Jaros262/zaverecny_projekt/code/simple_parts/bluetooth/setup/how_to_configure_and_pair_two_hc-05_bluetooth_modules_as_master_and_slave_at_commands_F2QwFNeicx.png

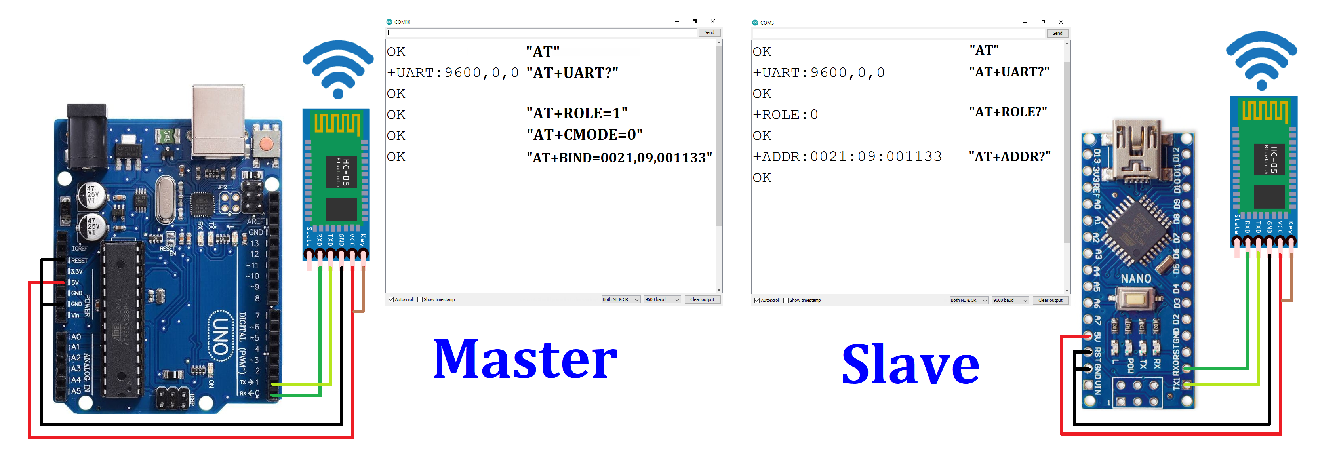
code/simple_parts/bluetooth/setup/how_to_configure_and_pair_two_hc-05_bluetooth_modules_as_master_and_slave_at_commands_F2QwFNeicx.png
