Jaros262/zaverecny_projekt/img_files/v1.1.png

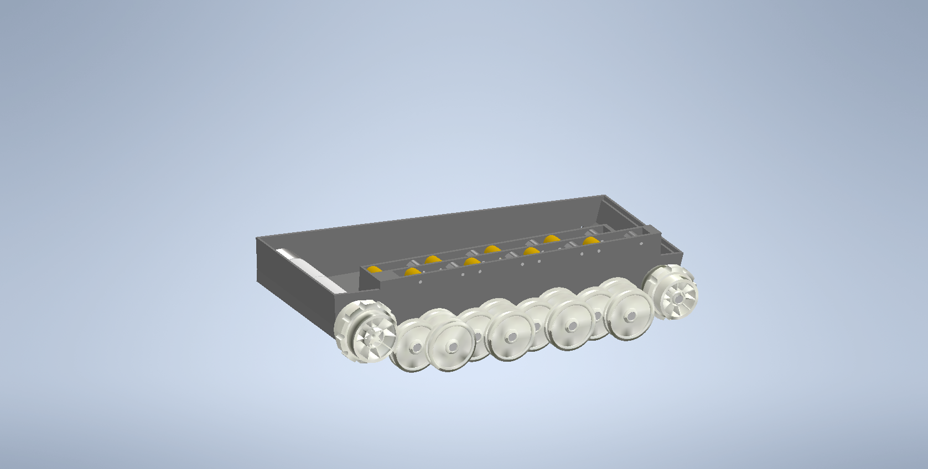
img_files/v1.1.png
