Jaros262/zaverecny_projekt/code/img/principOvladaniMotoru.png

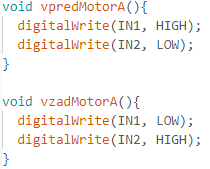
code/img/principOvladaniMotoru.png
