Jaros262/zaverecny_projekt/code/img/principServa.png

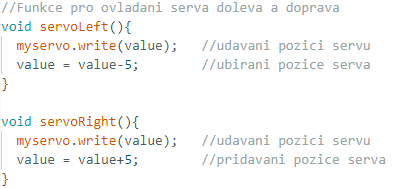
code/img/principServa.png
