Jaros262/zaverecny_projekt/img_files/battery.png

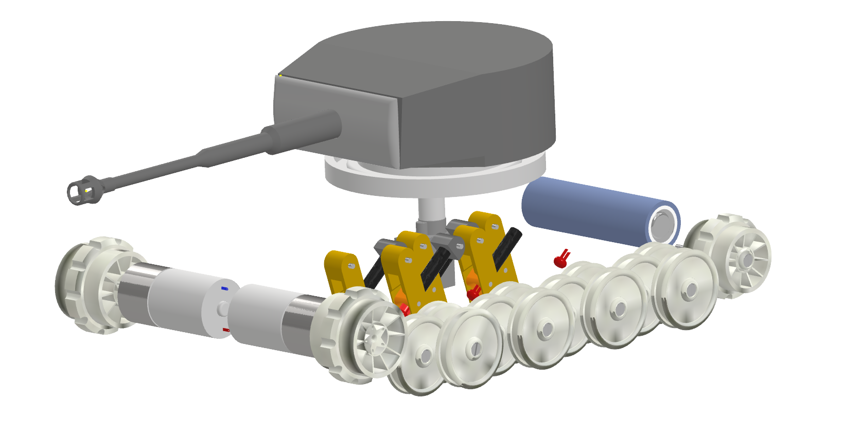
img_files/battery.png
