Jaros262/zaverecny_projekt/img_files/cele-rozdělané.png

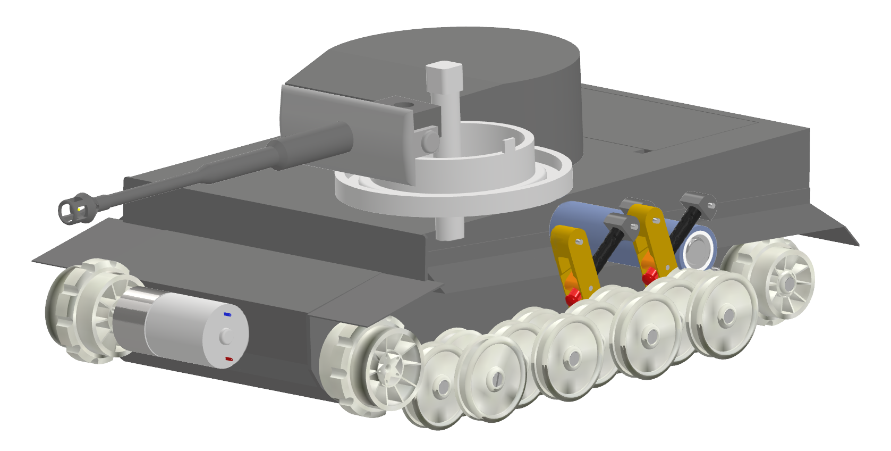
img_files/cele-rozdělané.png
