Jaros262/zaverecny_projekt/img_files/cele-s-popisy.png

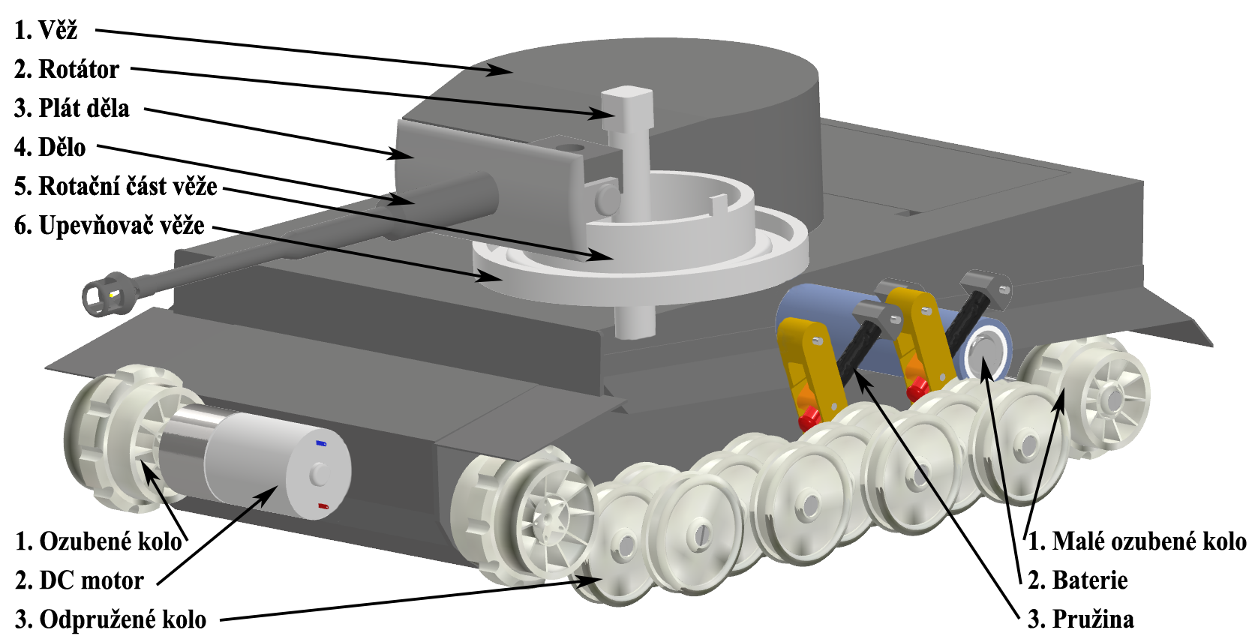
img_files/cele-s-popisy.png
