Jaros262/zaverecny_projekt/img_files/cele.png

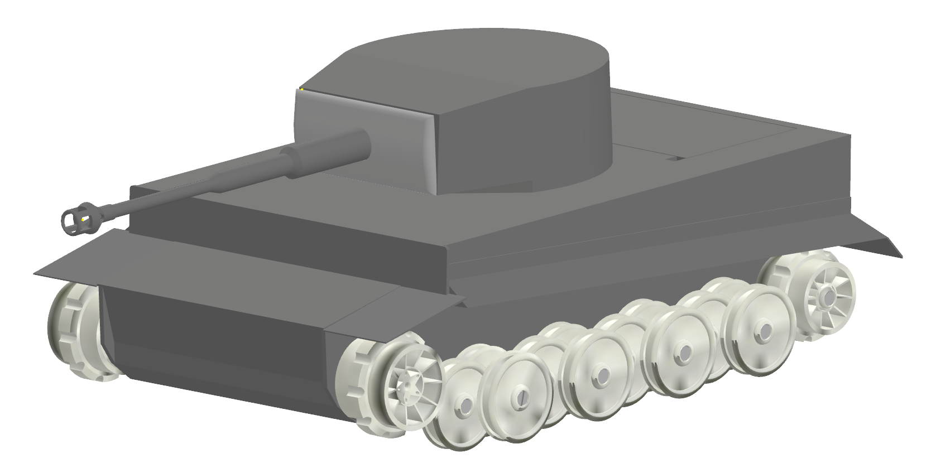
img_files/cele.png
