Jaros262/zaverecny_projekt/img_files/dolni.png

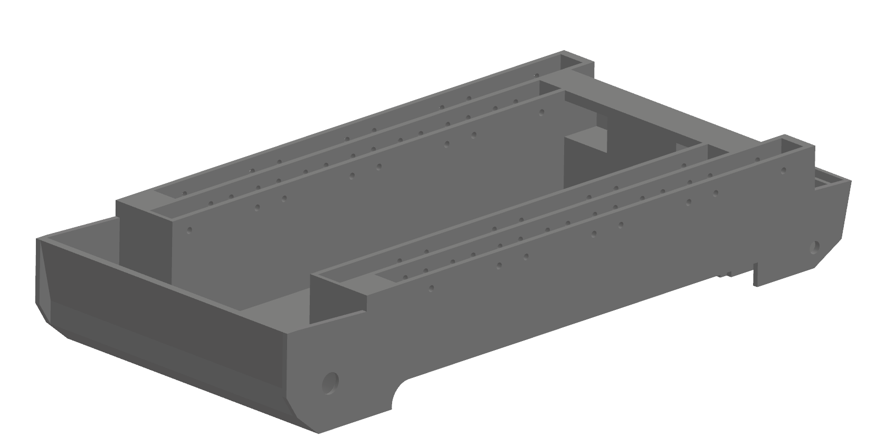
img_files/dolni.png
