Jaros262/zaverecny_projekt/img_files/dělo-plát.png

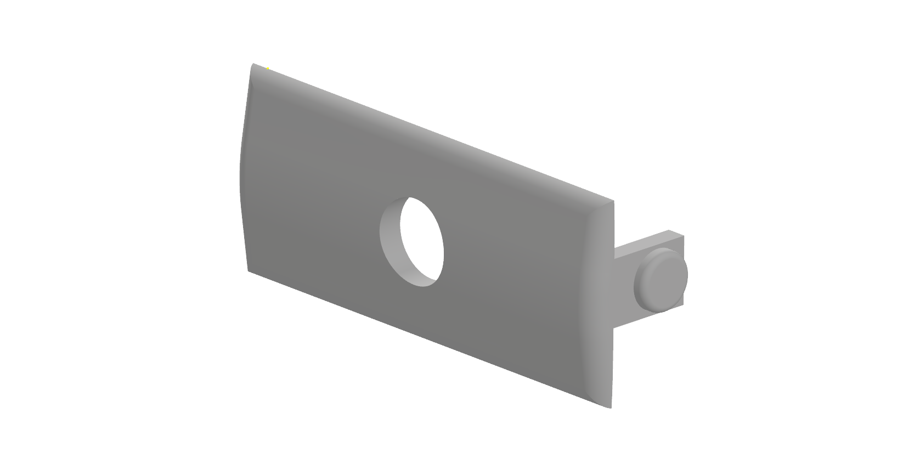
img_files/dělo-plát.png
