Jaros262/zaverecny_projekt/img_files/dělo.png

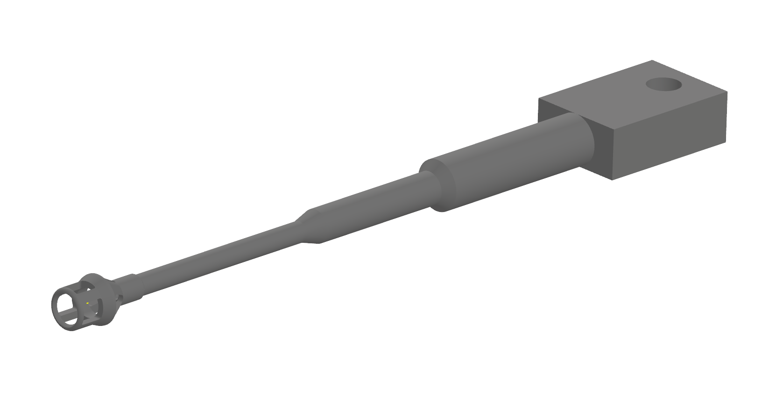
img_files/dělo.png
