Jaros262/zaverecny_projekt/img_files/horni.png

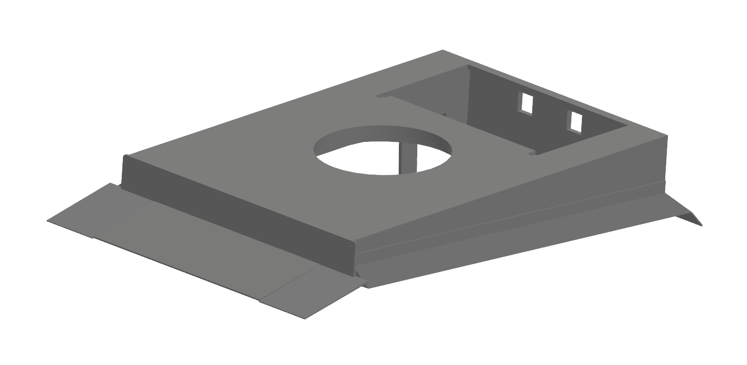
img_files/horni.png
