Jaros262/zaverecny_projekt/img_files/inside.png

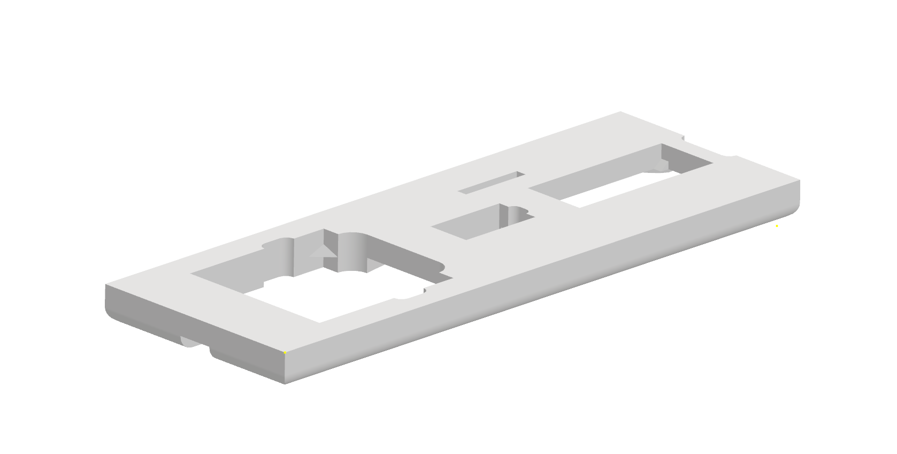
img_files/inside.png
