Jaros262/zaverecny_projekt/img_files/joystick_desk.png

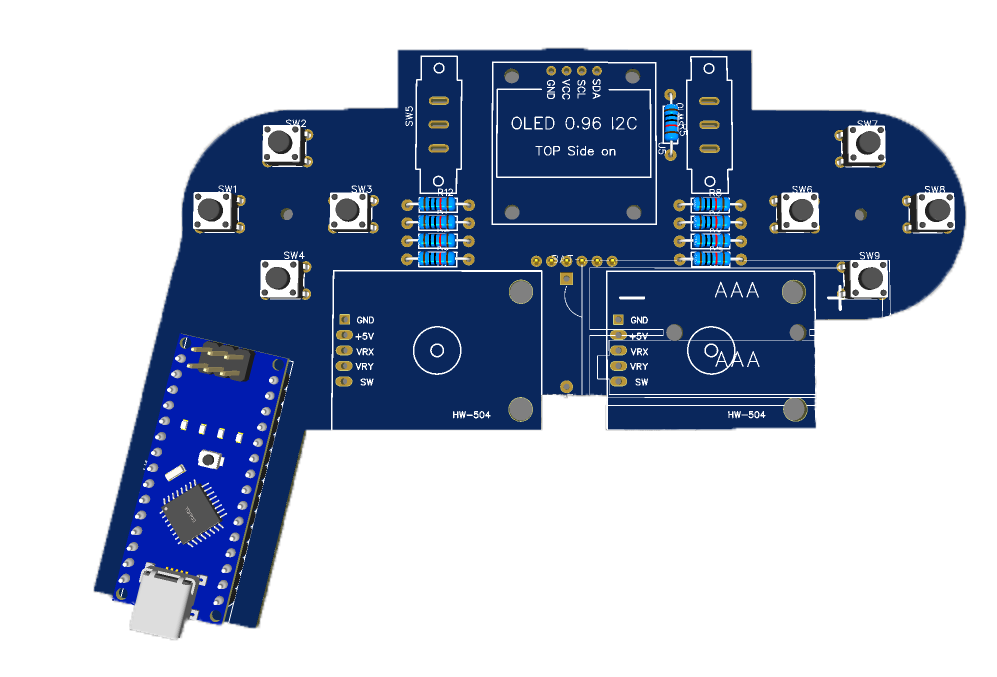
img_files/joystick_desk.png
