Jaros262/zaverecny_projekt/img_files/kolo.png

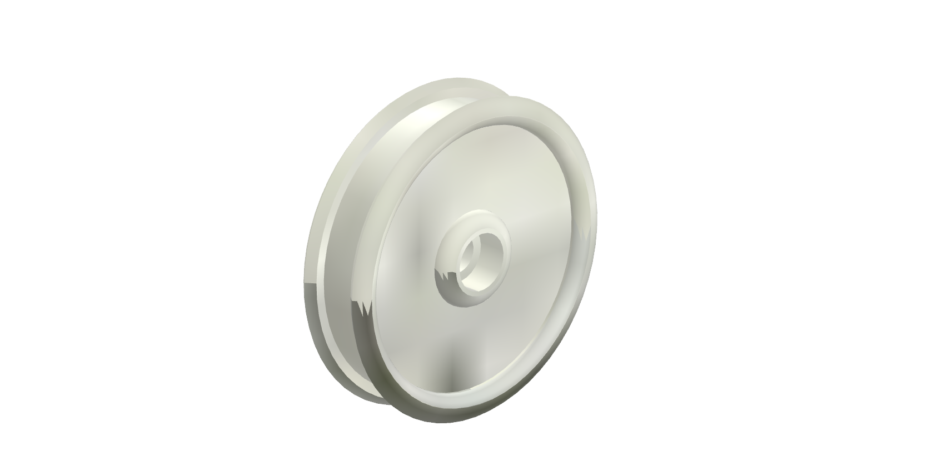
img_files/kolo.png
