Jaros262/zaverecny_projekt/img_files/minus-top-a-bot-a-vez.png

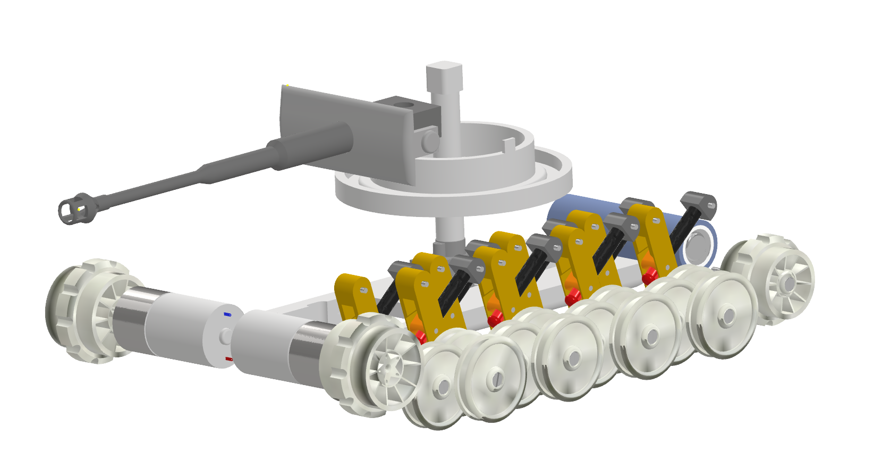
img_files/minus-top-a-bot-a-vez.png
