Jaros262/zaverecny_projekt/img_files/minus-top-a-bot.png

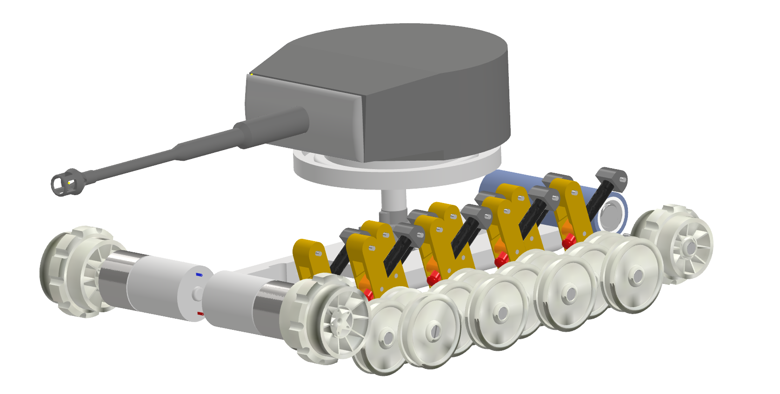
img_files/minus-top-a-bot.png
