Jaros262/zaverecny_projekt/img_files/minus-top.png

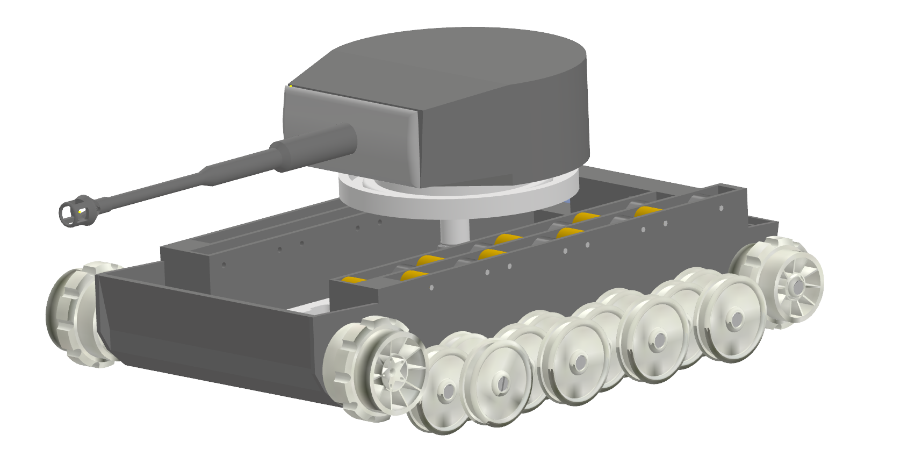
img_files/minus-top.png
