Jaros262/zaverecny_projekt/img_files/odpruzeni.png

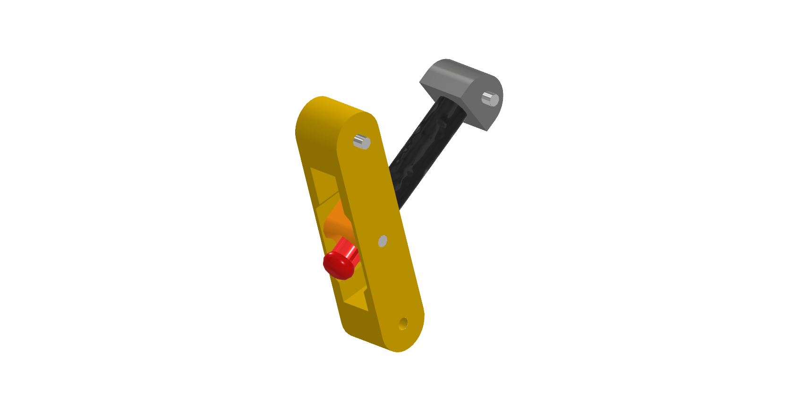
img_files/odpruzeni.png
