Jaros262/zaverecny_projekt/img_files/ozubene-kolo.png

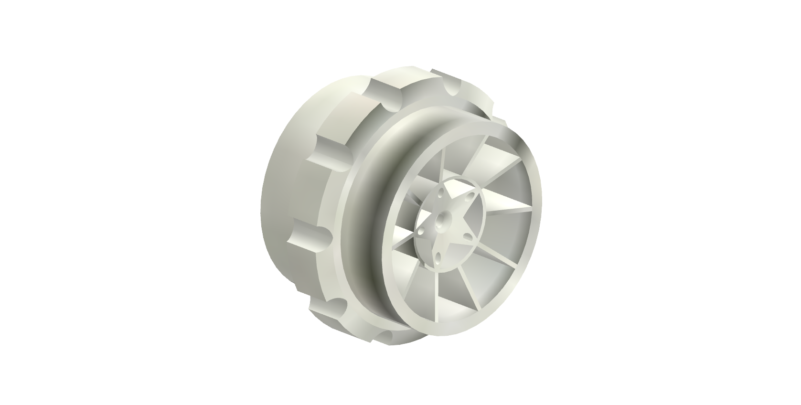
img_files/ozubene-kolo.png
