Jaros262/zaverecny_projekt/img_files/priklop.png

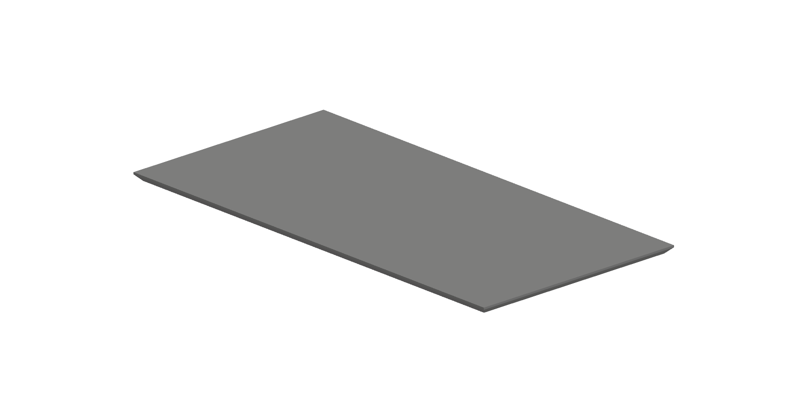
img_files/priklop.png
