Jaros262/zaverecny_projekt/img_files/rotator.png

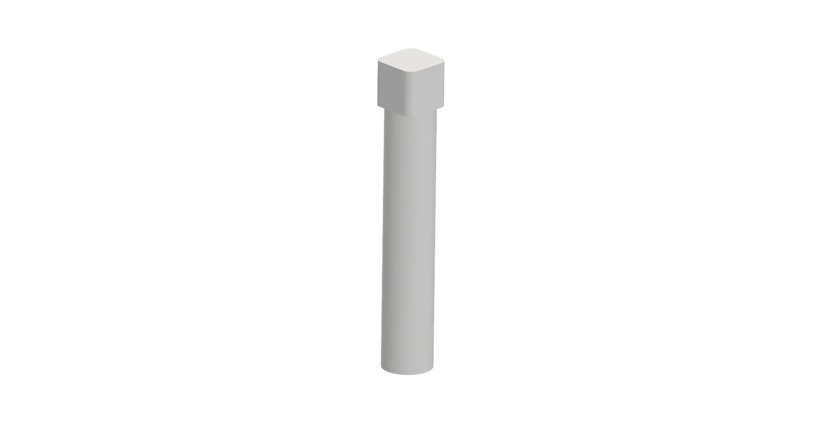
img_files/rotator.png
