Jaros262/zaverecny_projekt/img_files/upevnovac.png

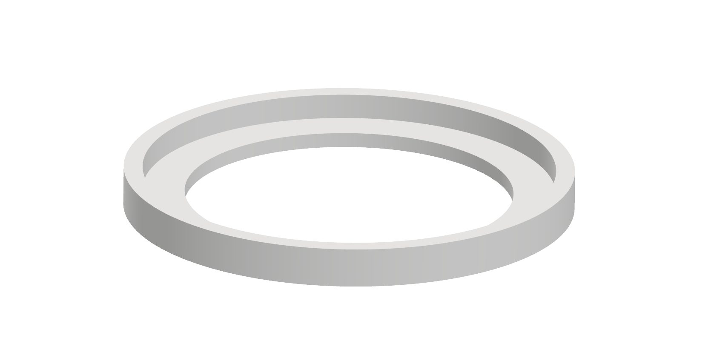
img_files/upevnovac.png
