Jaros262/zaverecny_projekt/img_files/v1.2.png

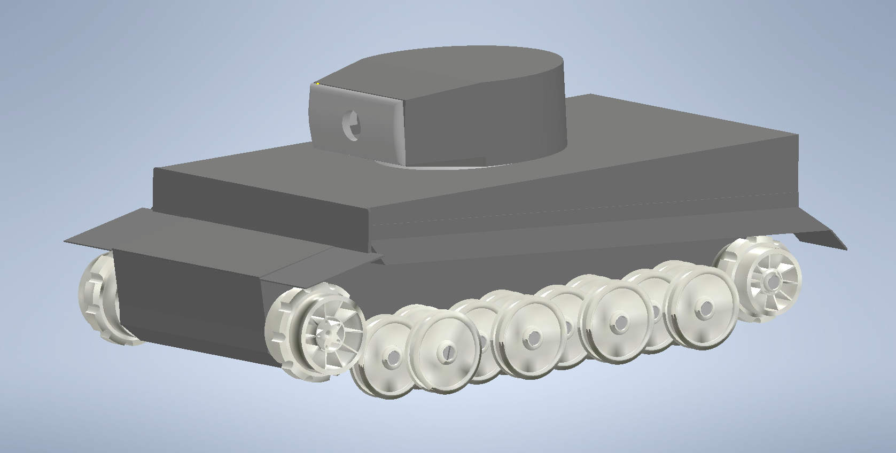
img_files/v1.2.png
