Jaros262/zaverecny_projekt/img_files/v1.2_XRAY.png

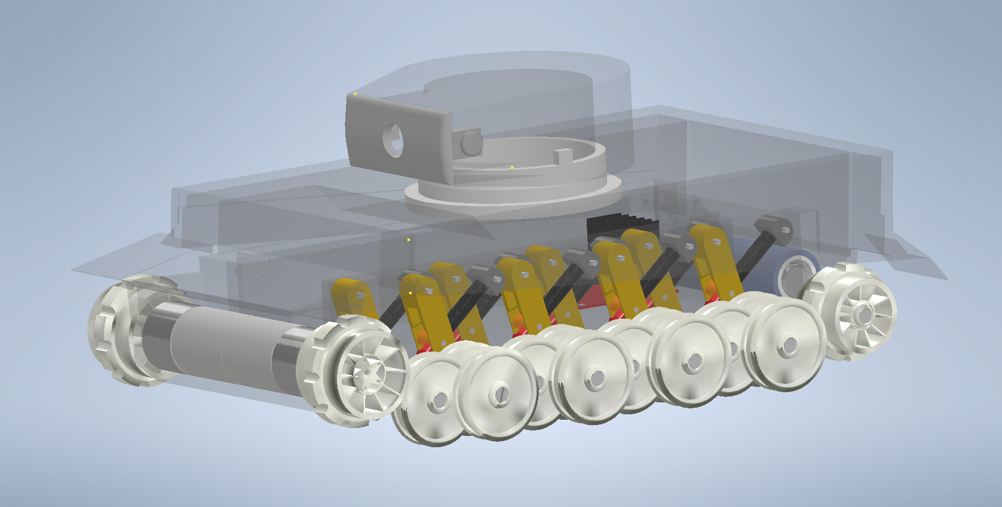
img_files/v1.2_XRAY.png
