Jaros262/zaverecny_projekt/img_files/vez.png

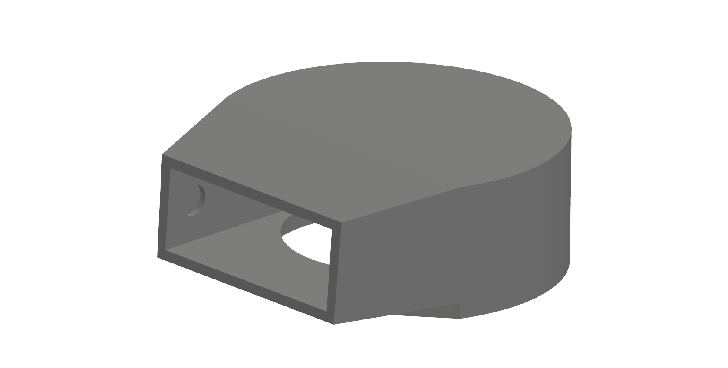
img_files/vez.png
