Jaros262/zaverecny_projekt/img_files/věž-rotate.png

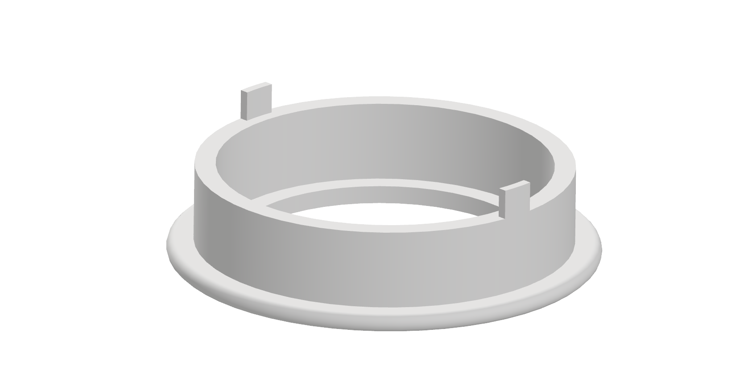
img_files/věž-rotate.png
