Jaros262/zaverecny_projekt/model/schémata/5df1a9c784468c0f967bb183d96bbcd3.jpg

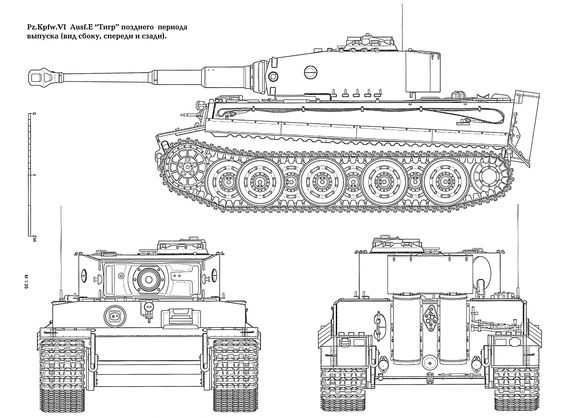
model/schémata/5df1a9c784468c0f967bb183d96bbcd3.jpg
