Jaros262/zaverecny_projekt/model/schémata/06c04c4e661aaf2cee95b31e4a906c01.jpg

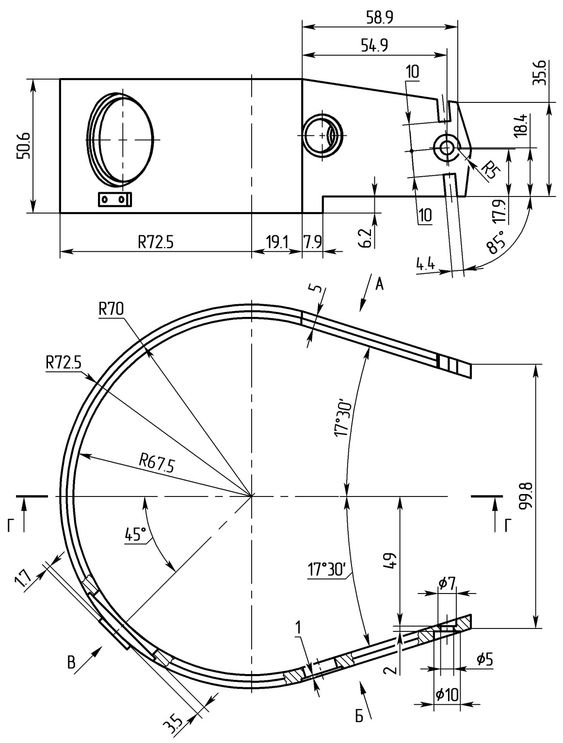
model/schémata/06c04c4e661aaf2cee95b31e4a906c01.jpg
