Jaros262/zaverecny_projekt/model/schémata/abhi-jindal-1.jpg

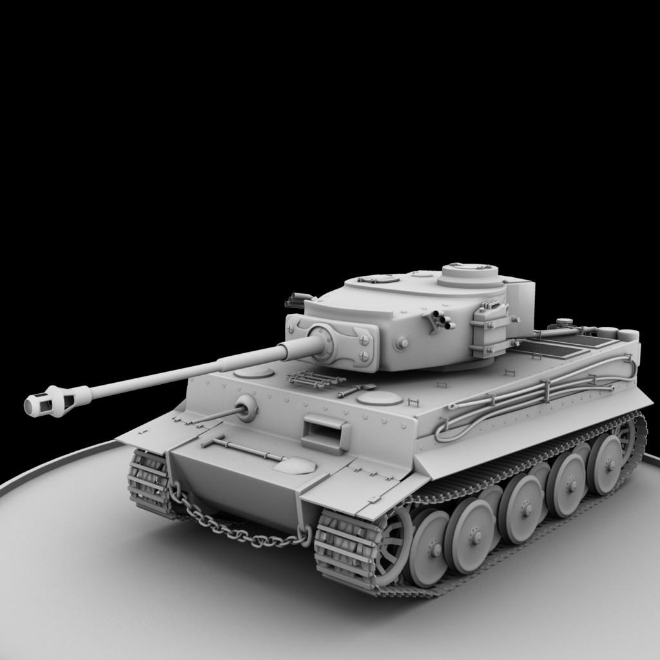
model/schémata/abhi-jindal-1.jpg
