Jaros262/zaverecny_projekt/model/schémata/inspirace/20141102_222440_resized.jpg

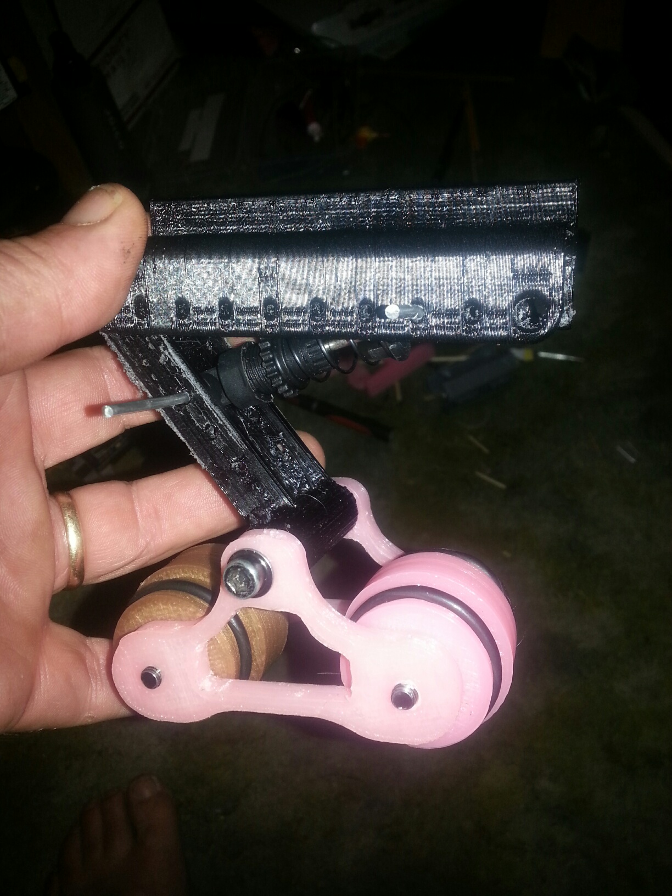
model/schémata/inspirace/20141102_222440_resized.jpg
