Jaros262/zaverecny_projekt/model/schémata/tiger_cutaway.jpg.9aa13aeb91908b706b345edadf08b43d.jpg

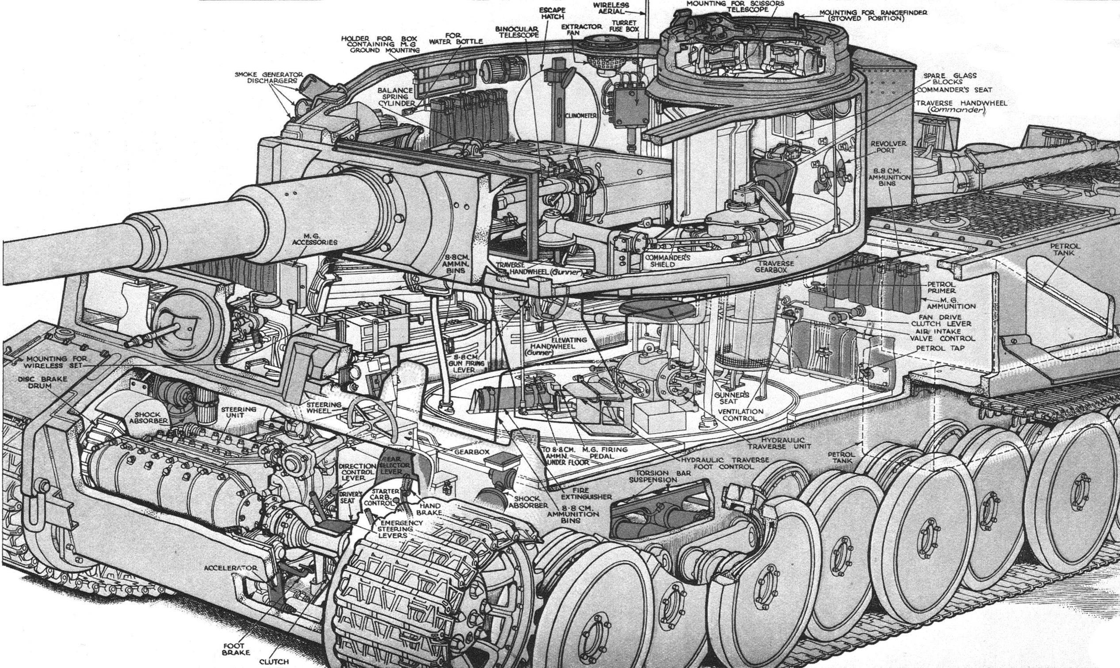
model/schémata/tiger_cutaway.jpg.9aa13aeb91908b706b345edadf08b43d.jpg
